tebl/A2600-Keyboard/gallery/2021-03-12 20.48.29.jpg

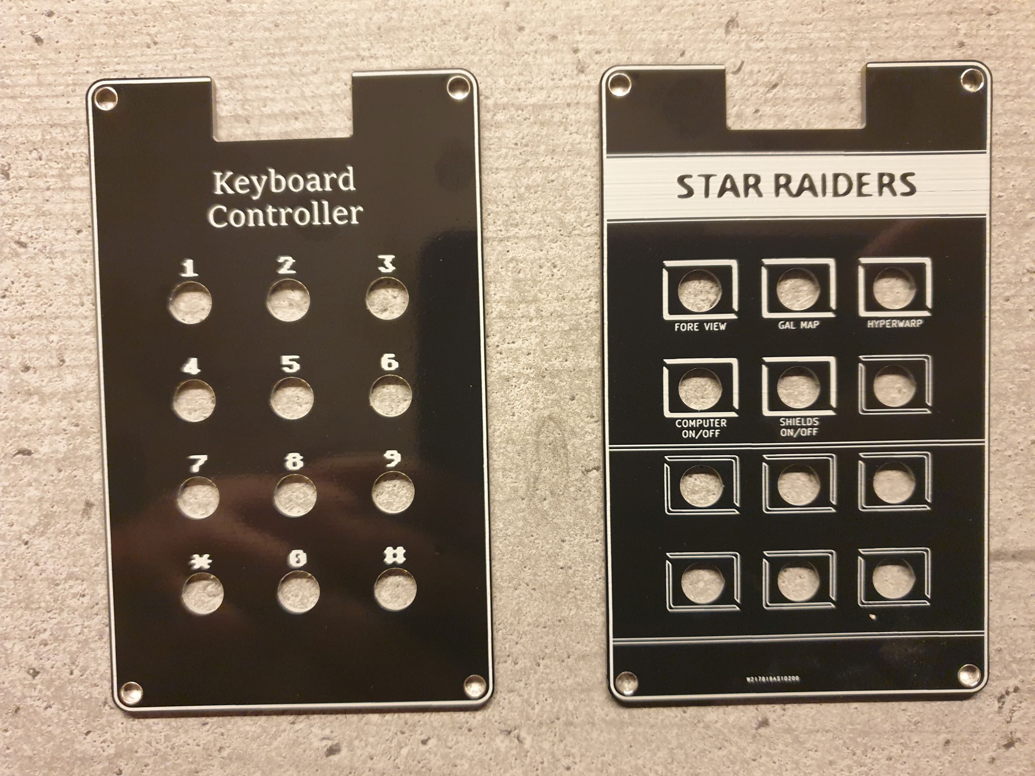
gallery/2021-03-12 20.48.29.jpg
