tebl/A2600-Keyboard/gallery/2021-03-12 21.04.39.jpg

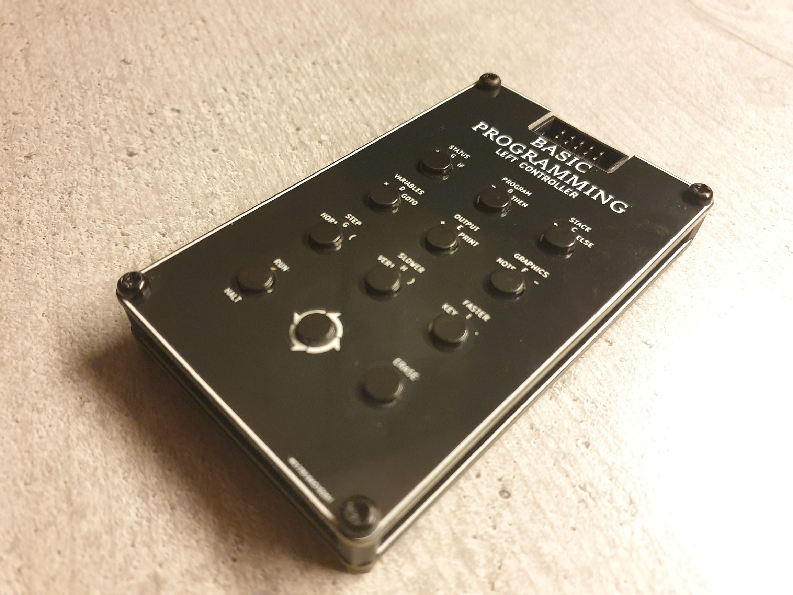
gallery/2021-03-12 21.04.39.jpg
