tebl/A2600-Keyboard/gallery/A2600 Faceplate Basic Left.png

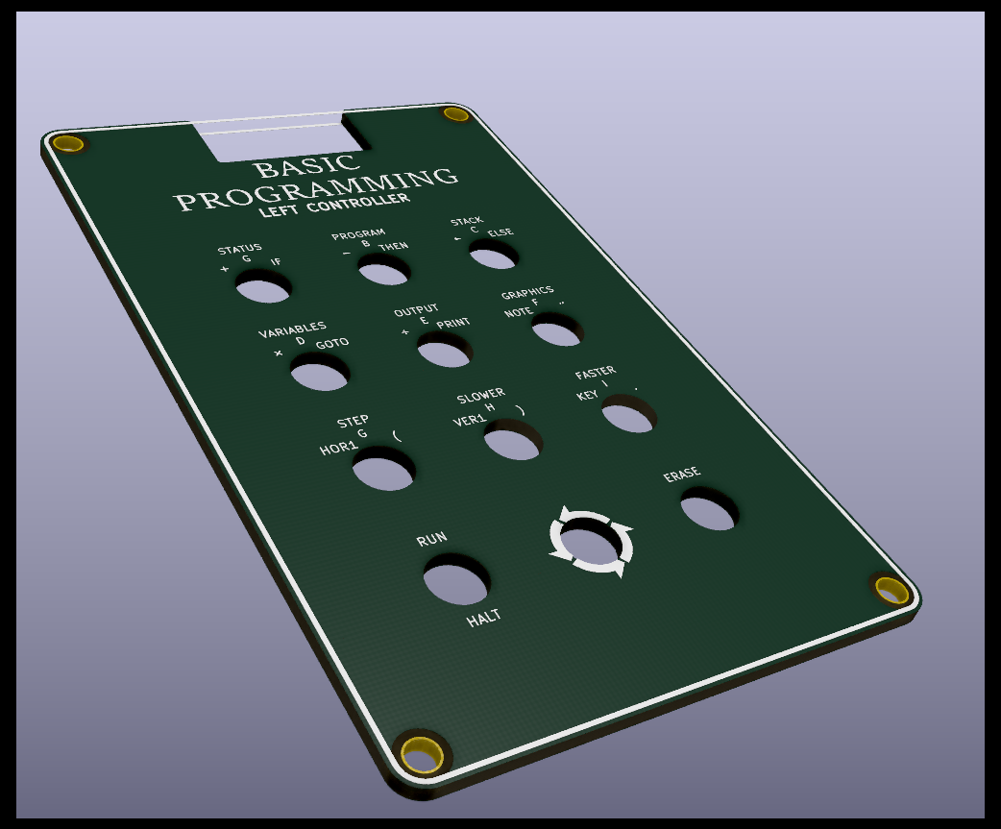
gallery/A2600 Faceplate Basic Left.png
