tebl/A2600-Keyboard/gallery/A2600 Faceplate SR.png

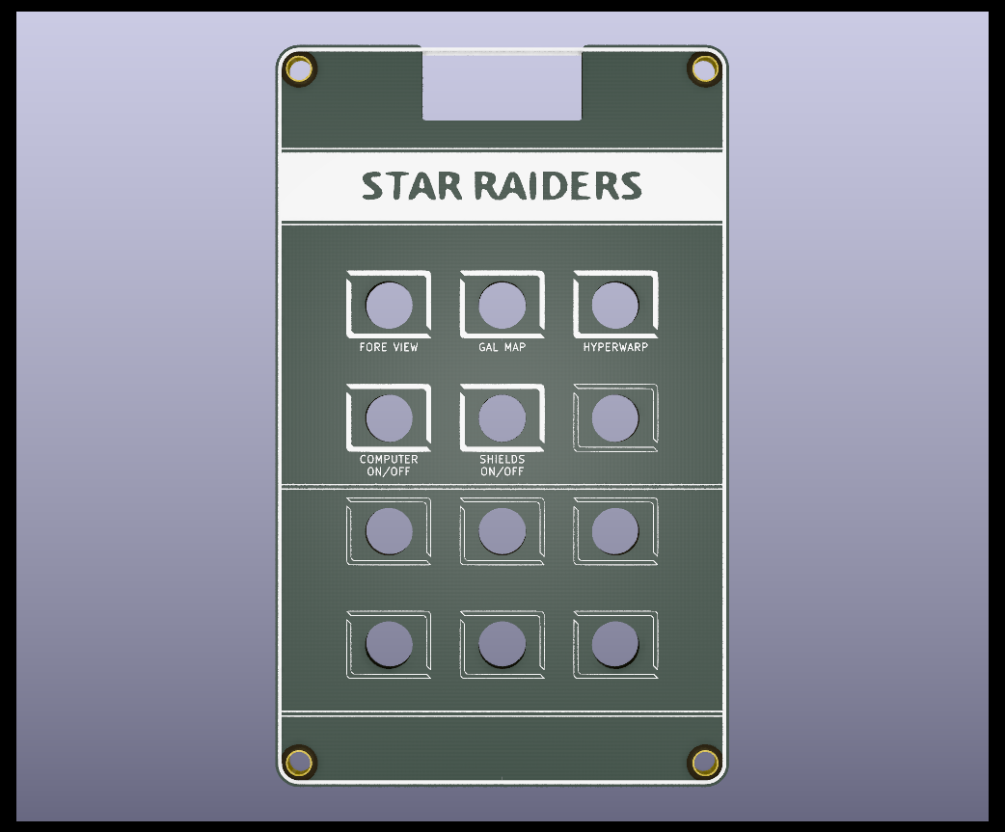
gallery/A2600 Faceplate SR.png
