tebl/A2600-Keyboard/gallery/A2600 Faceplate synthcart.png

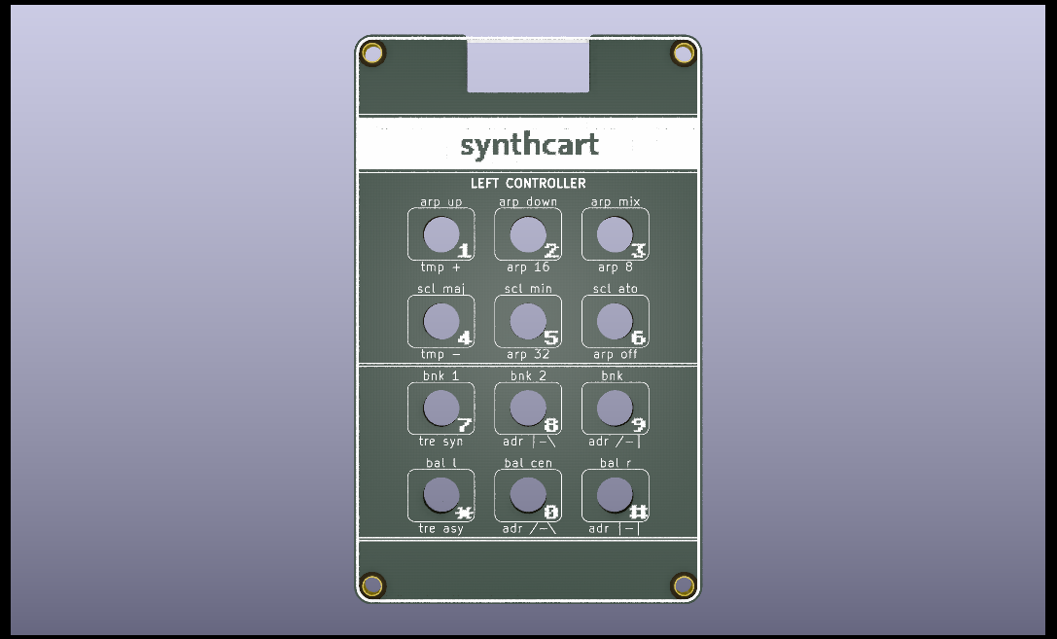
gallery/A2600 Faceplate synthcart.png
