tebl/A2600-Keyboard/gallery/A2600 Faceplate.png

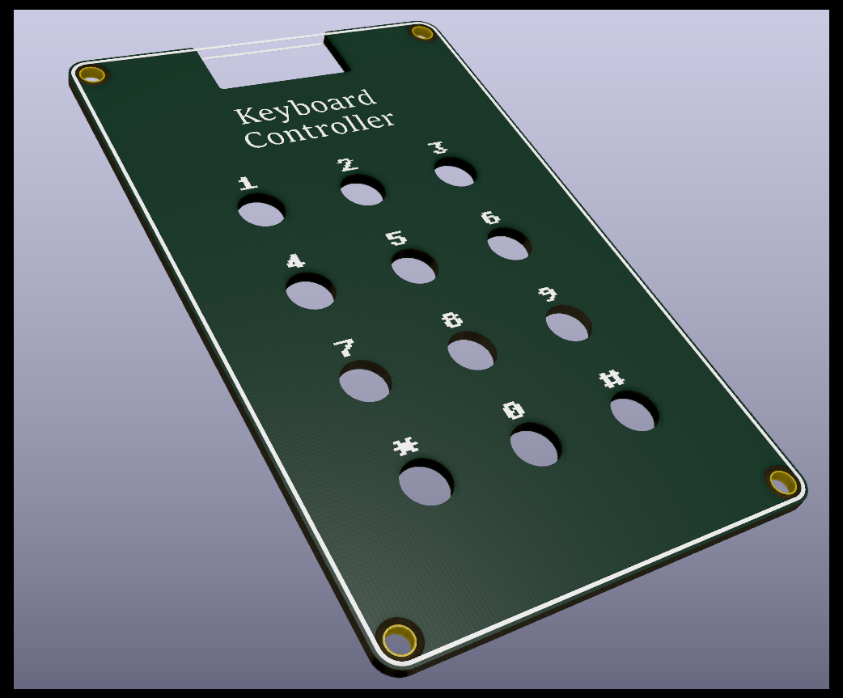
gallery/A2600 Faceplate.png
