tebl/A2600-Keyboard/gallery/A2600 Keyboard2.png

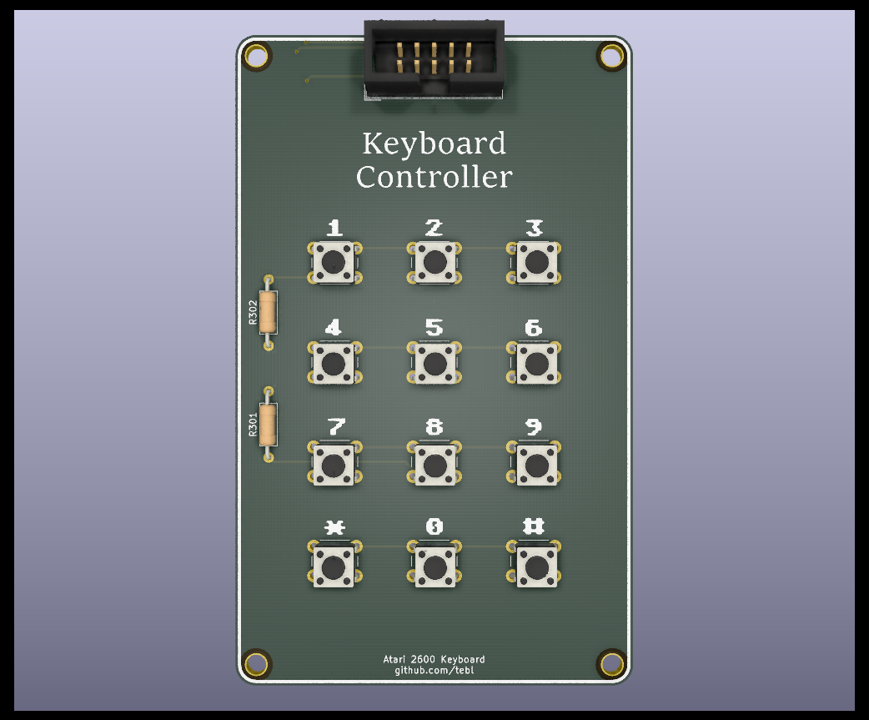
gallery/A2600 Keyboard2.png
