tebl/A2600-Keyboard/gallery/A2600 Keyboard.png

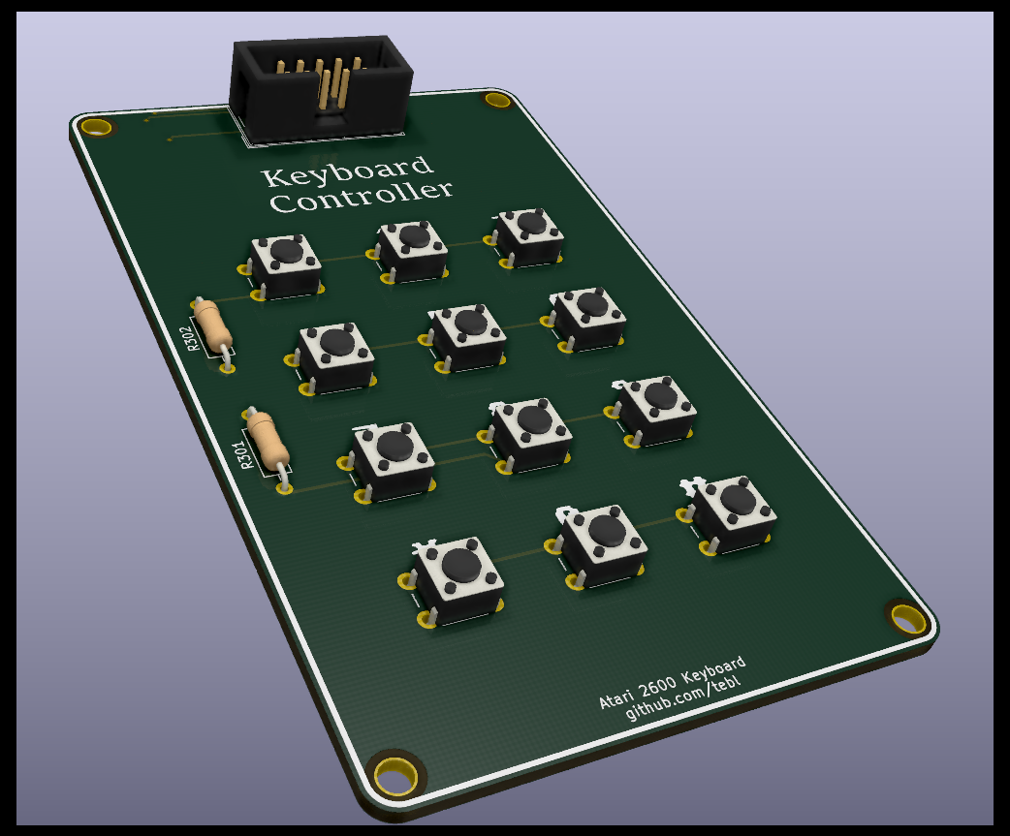
gallery/A2600 Keyboard.png
